vinaykumarhegde/BeoBot3/firmware/arduino_mega/commands.h

/* Define single-letter commands that will be sent by the PC over the
   serial link.
*/

#ifndef COMMANDS_H
#define COMMANDS_H

#define ANALOG_READ    'a'
#define GET_BAUDRATE   'b'
#define PIN_MODE       'c'
#define DIGITAL_READ   'd'
#define READ_ENCODERS  'e'
#define MOTOR_SPEEDS   'm'
#define RESET_ENCODERS 'r'
#define SERVO_WRITE    's'
#define SERVO_READ     't'
#define UPDATE_PID     'u'
#define DIGITAL_WRITE  'w'
#define ANALOG_WRITE   'x'
#define LEFT            0
#define RIGHT           1

#ifndef PING
#define PING           'p'
#else
#undef PING
#define PING           'p'
#endif

// URM04 Sensor command:
#define URM04          'q'

#endif
